simoninns/Acorn-Master-Cartridge-Breakout/Cartridge/PDF/Cartridge Header-F.Cu.pdf

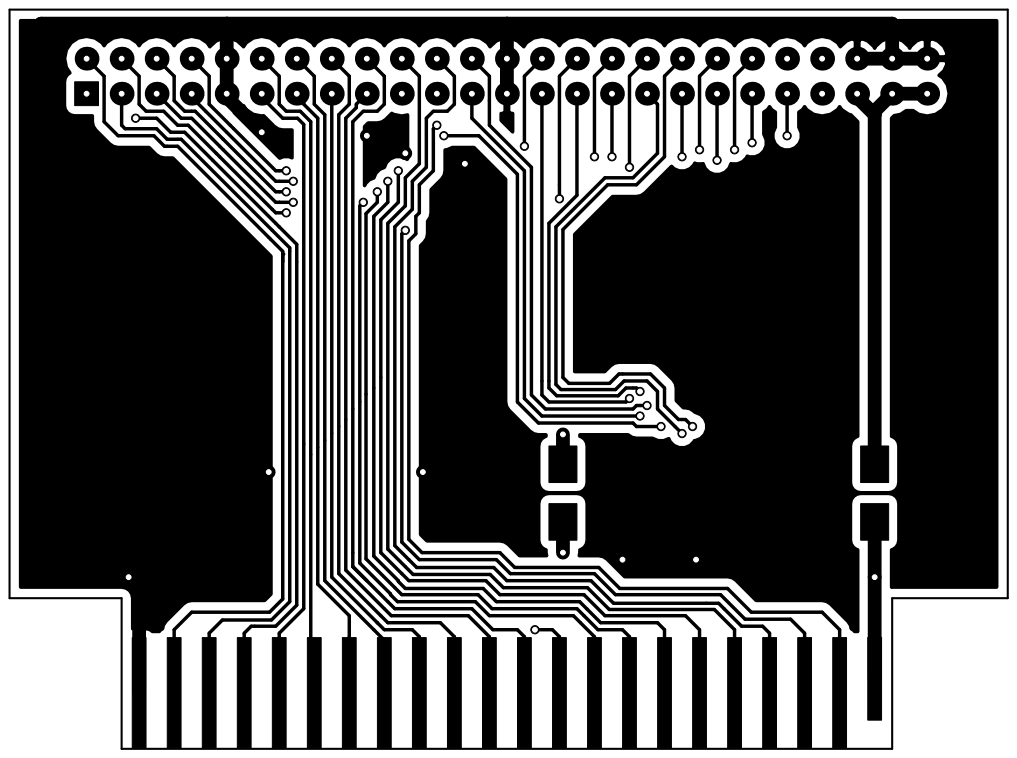
[picture p14: page 1]
