simoninns/Acorn-Master-Cartridge-Breakout/Cartridge/PDF/Cartridge Header-F.Mask.pdf

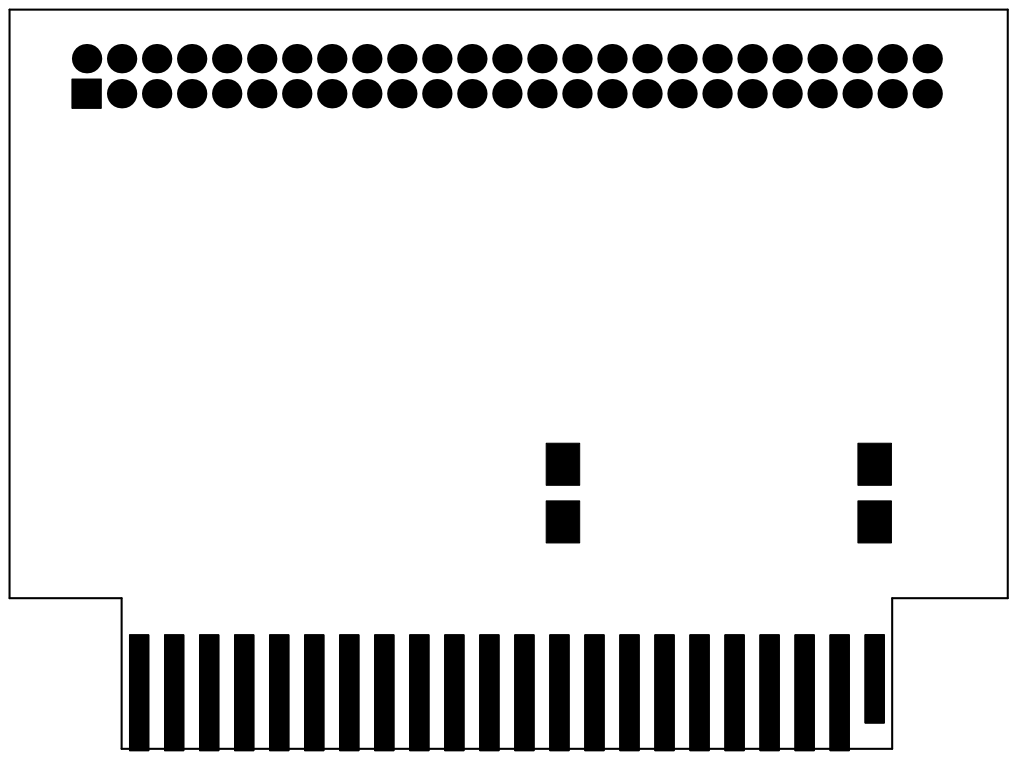
[picture p15: page 1]
