simoninns/Acorn-Master-Cartridge-Breakout/Cartridge/PDF/Cartridge Header-F.SilkS.pdf

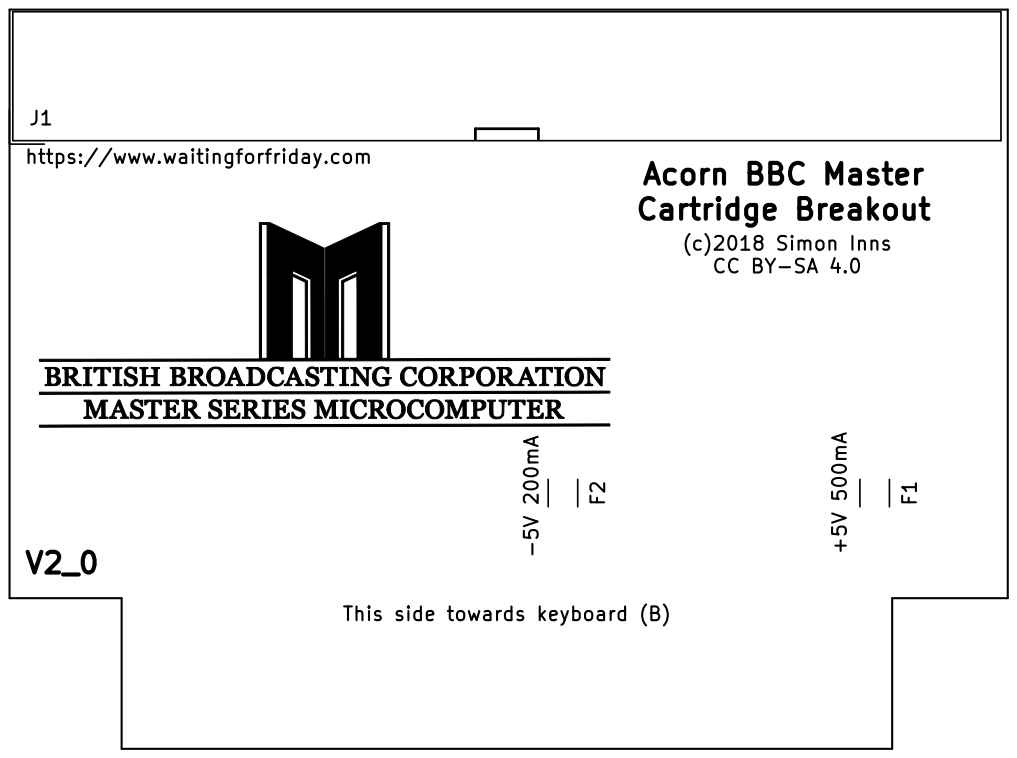
[picture p16: page 1]
