simoninns/Acorn-Master-Cartridge-Breakout/Cartridge/PDF/Cartridge Header.pdf

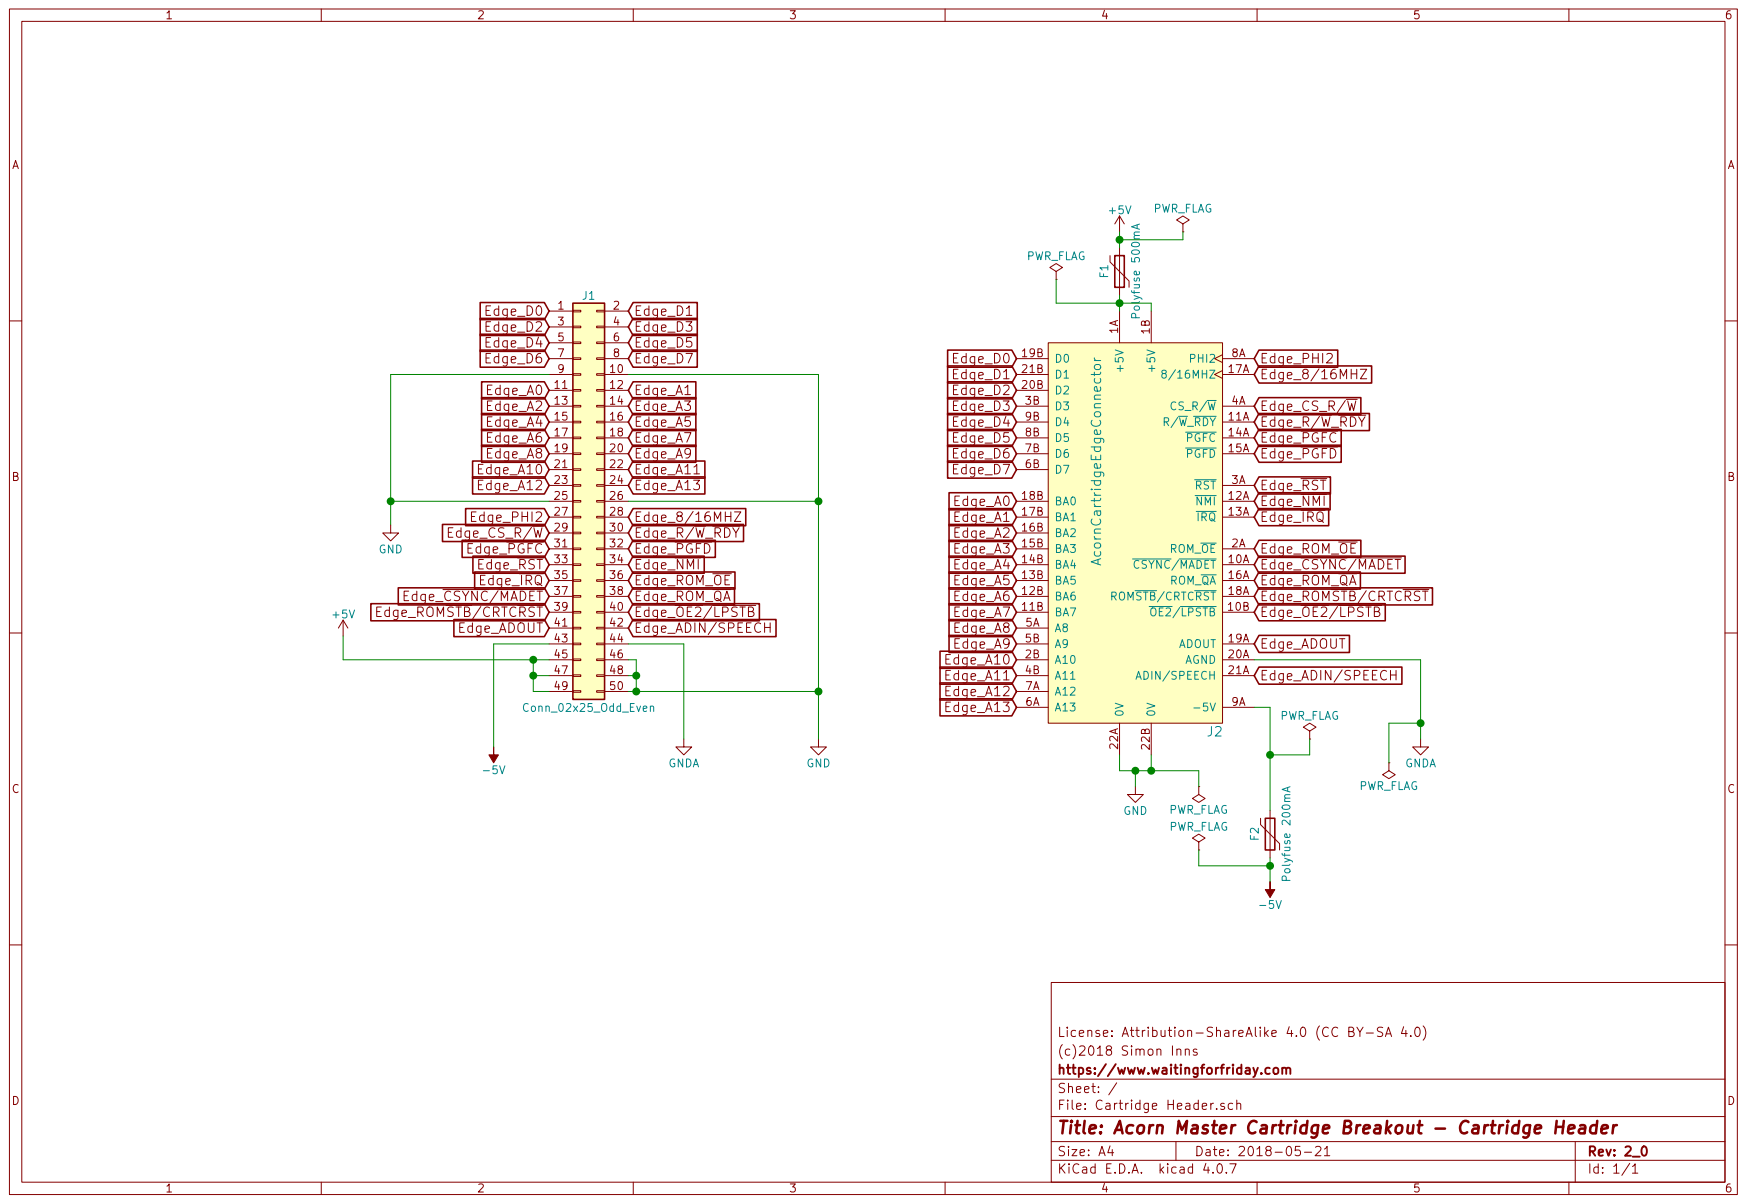
[picture p17: page 1]
